danaibavishi/iso-damper/04_compliant_puck/iterations/v3_straight_pedestal.stl

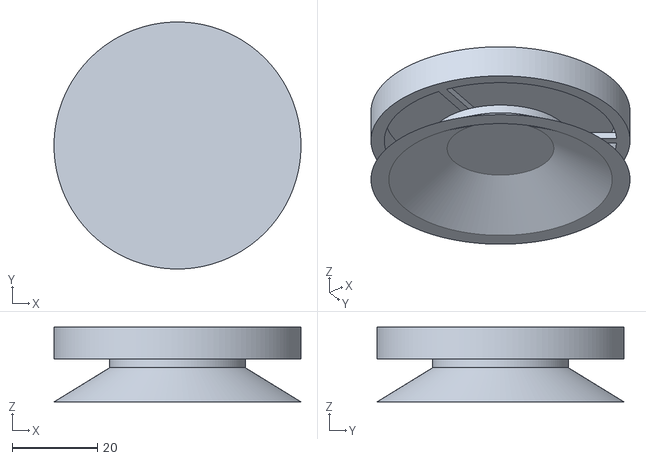
[picture p24: CAD file, 2026-04-03]
04_compliant_puck/iterations/v3_straight_pedestal.stl
57.9 x 57.9 x 17.5
